qinno/qEdge-UI/Software/examples/HwTestApp/data/qEdgeWallpaperScreen.png

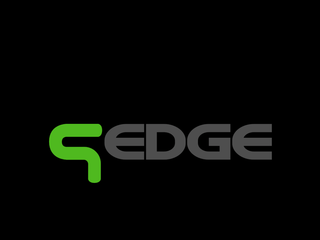
Software/examples/HwTestApp/data/qEdgeWallpaperScreen.png
