qinno/qEdge-UI/Software/examples/HwTestApp/data/HwTestAppMenueScreen.png

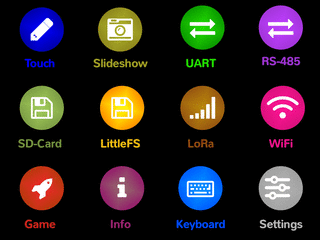
Software/examples/HwTestApp/data/HwTestAppMenueScreen.png
