qinno/qEdge-UI/Software/examples/HwTestApp/data/qEdgeBootScreen.png

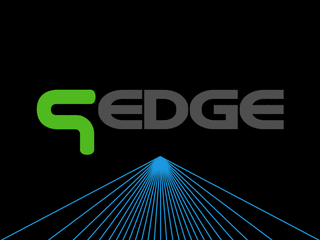
Software/examples/HwTestApp/data/qEdgeBootScreen.png
