qinno/qEdge-UI/Software/examples/HwTestApp/data/qEdgeIdleScreen.png

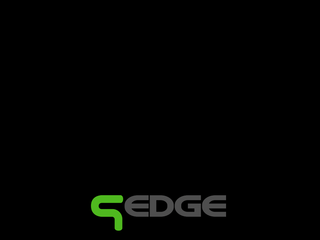
Software/examples/HwTestApp/data/qEdgeIdleScreen.png
