qinno/qEdge-UI/Software/examples/HwTestApp/SDcontent/aviation2.png

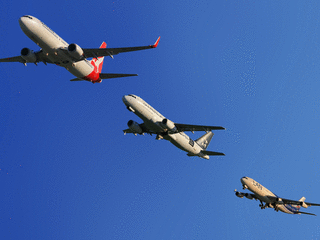
Software/examples/HwTestApp/SDcontent/aviation2.png
