qinno/qEdge-UI/Software/examples/HwTestApp/SDcontent/aviation.png

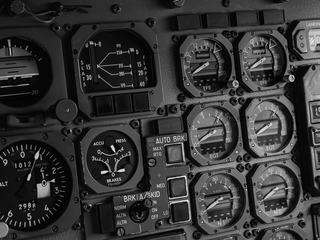
Software/examples/HwTestApp/SDcontent/aviation.png
