qinno/qEdge-UI/Software/examples/HwTestApp/SDcontent/avionics3.png

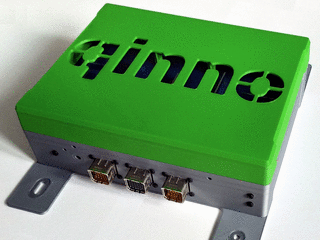
Software/examples/HwTestApp/SDcontent/avionics3.png
