qinno/qEdge-UI/Software/examples/HwTestApp/SDcontent/boot.png

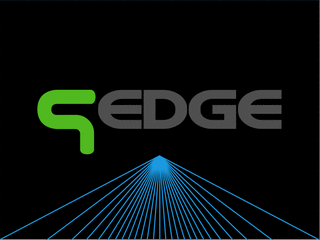
Software/examples/HwTestApp/SDcontent/boot.png
