qinno/qEdge-UI/Software/examples/HwTestApp/SDcontent/caution.png

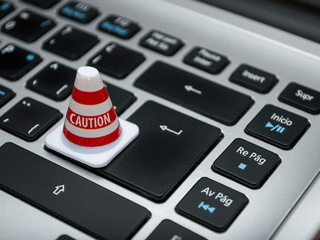
Software/examples/HwTestApp/SDcontent/caution.png
