qinno/qEdge-UI/Software/examples/HwTestApp/SDcontent/cavitau2.png

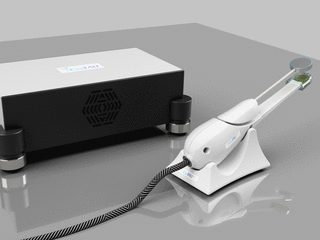
Software/examples/HwTestApp/SDcontent/cavitau2.png
