qinno/qEdge-UI/Software/examples/HwTestApp/SDcontent/contacts.png

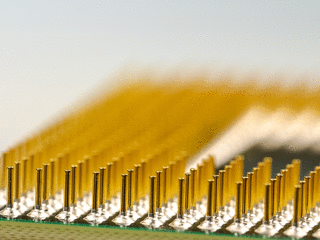
Software/examples/HwTestApp/SDcontent/contacts.png
