qinno/qEdge-UI/Software/examples/HwTestApp/SDcontent/frontpanel.png

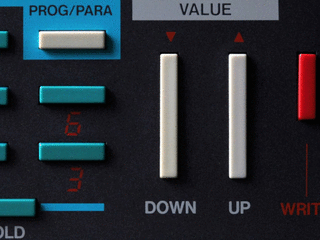
Software/examples/HwTestApp/SDcontent/frontpanel.png
