qinno/qEdge-UI/Software/examples/HwTestApp/SDcontent/heating.png

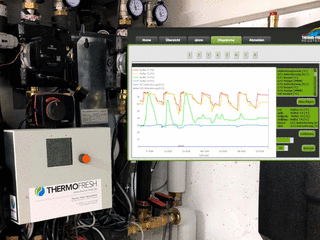
Software/examples/HwTestApp/SDcontent/heating.png
