qinno/qEdge-UI/Software/examples/HwTestApp/SDcontent/impression.png

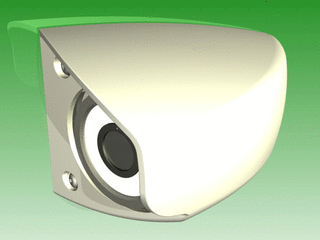
Software/examples/HwTestApp/SDcontent/impression.png
