qinno/qEdge-UI/Software/examples/HwTestApp/SDcontent/keyboard.png

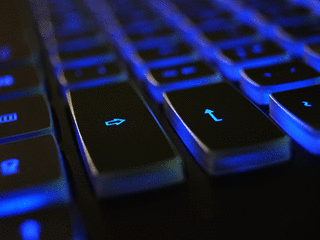
Software/examples/HwTestApp/SDcontent/keyboard.png
