qinno/qEdge-UI/Software/examples/HwTestApp/SDcontent/notebook.png

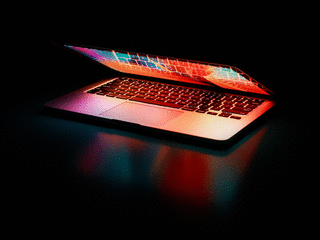
Software/examples/HwTestApp/SDcontent/notebook.png
