qinno/qEdge-UI/Software/examples/HwTestApp/SDcontent/pcb2.png

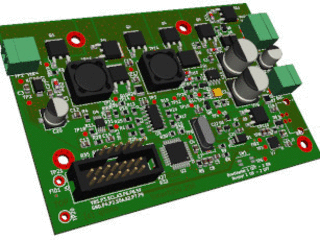
Software/examples/HwTestApp/SDcontent/pcb2.png
