qinno/qEdge-UI/Software/examples/HwTestApp/SDcontent/pcb.png

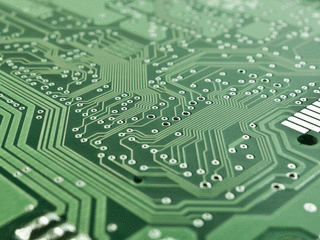
Software/examples/HwTestApp/SDcontent/pcb.png
