qinno/qEdge-UI/Software/examples/HwTestApp/SDcontent/product2.png

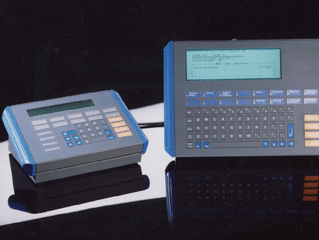
Software/examples/HwTestApp/SDcontent/product2.png
