qinno/qEdge-UI/Software/examples/HwTestApp/SDcontent/python.png

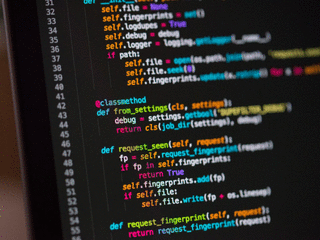
Software/examples/HwTestApp/SDcontent/python.png
