qinno/qEdge-UI/Software/examples/HwTestApp/SDcontent/screen.png

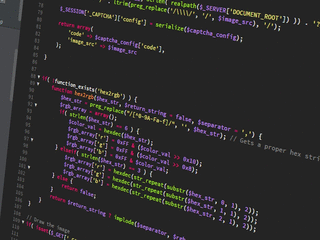
Software/examples/HwTestApp/SDcontent/screen.png
