qinno/qEdge-UI/Software/examples/HwTestApp/SDcontent/sketch2.png

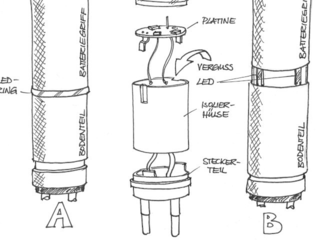
Software/examples/HwTestApp/SDcontent/sketch2.png
